emilyanthony4244/Super-2027-Swadge-HW/Swadge-HW/3D-Print/Wub-Tank-Proto.step

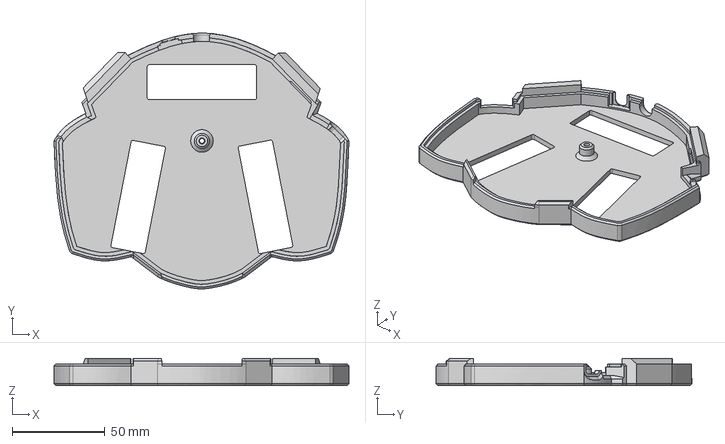
[picture p16: CAD file, 2026-04-04]
Swadge-HW/3D-Print/Wub-Tank-Proto.step
159.3 x 138.2 x 14.6 mm
